windflyfree/Trinus_3D_Printer/Klipper_config/TT_leds.cfg

[led MY_LED]
RED_PIN:!PC4
initial_RED: 1.0

[gcode_macro LEDOFF]
gcode:  SET_LED LED=MY_LED RED=0  

[gcode_macro LEDMIN]
gcode:  SET_LED LED=MY_LED RED=0.1

[gcode_macro LEDMAX]
gcode:  SET_LED LED=MY_LED RED=1

[gcode_macro LIGHTS_WARMING]
gcode: 
      SET_LED LED=MY_LED RED=0.2
      G4 P500
      SET_LED LED=MY_LED RED=1
      G4 P500

[gcode_macro LIGHTS_HOT]
gcode:  
    SET_LED LED=MY_LED RED=0.5
    G4 P1500
    SET_LED LED=MY_LED RED=1
    G4 P1500
