windflyfree/Trinus_3D_Printer/Klipper_config/T_leds.cfg

[output_pin LED_pin]
pin: !PC4
pwm: True
value: 0

[gcode_macro LEDOFF]
gcode:  SET_PIN PIN=LED_pin VALUE=0

[gcode_macro LEDMIN]
gcode:  SET_PIN PIN=LED_pin VALUE=.1  CYCLE_TIME=3

[gcode_macro LEDMAX]
gcode:  SET_PIN PIN=LED_pin VALUE=1

[gcode_macro LIGHTS_WARMING]
gcode:  SET_PIN PIN=LED_pin VALUE=.1  CYCLE_TIME=1

[gcode_macro LIGHTS_HOT]
gcode:  SET_PIN PIN=LED_pin VALUE=.2  CYCLE_TIME=5
